Rustaphor/LightRelay4Camping/Sims/LSenseComparator_inverted.cir

[Main]
FileType=CIR
Version=12.00
Program=Micro-Cap
Component Version=10.00
Shape Version=11.00
Screen=1707,960
MCAPVersion=12.2.0.5
Key ID=Demo
NLCnt=60
TXCnt=10

[shapedef]
Name=Arrow
Line=-16,0,24,0
PolyClosed=4
PolyLine=24,0
PolyLine=24,0
PolyLine=16,-4
PolyLine=16,4

[shapedef]
Name=Capacitor
Line=0,0,22,0
Line=22,-8,22,8
Line=26,-8,26,8
Line=26,0,48,0
Current=32,12,16,12

[shapedef]
Name=Fixed
Line=8,0,32,0
Line=8,0,0,-8
Line=8,0,0,8

[shapedef]
Name=Ground
Line=0,0,12,0
Line=12,-8,12,8
Line=18,-4,18,4
Line=24,0,24,0

[shapedef]
Name=Minus.root
Line=-2,0,2,0

[shapedef]
Name=Opamp5
Root="Opamp.root",0,0,0
Root="Plus.root",25,-4,0
Root="Minus.root",25,52,0
Line=32,56,32,34
Line=32,-8,32,13

[shapedef]
Name=Opamp.root
Line=0,48,6,48
Line=0,0,5,0
Line=6,-4,6,52
Line=6,-4,48,24
Line=6,52,48,24
Line=48,24,72,24
Line=10,12,14,12
Line=12,10,12,14
Line=10,36,14,36
Line=4,0,6,0

[shapedef]
Name=Plus.root
Line=-2,0,2,0
Line=0,-2,0,2

[shapedef]
Name=Pot
Line=0,0,12,0
Line=12,0,14,-4
Line=14,-4,18,4
Line=18,4,22,-4
Line=22,-4,26,4
Line=26,4,30,-4
Line=30,-4,34,4
Line=34,4,36,0
Line=36,0,48,0
PolyClosed=4
PolyLine=24,4
PolyLine=24,4
PolyLine=22,8
PolyLine=26,8
Line=24,8,24,16

[shapedef]
Name=Pulse_Source
Root="Vsource.root",0,0,0
Line=20,-4,20,0
Line=20,0,26,0
Line=26,0,26,4

[shapedef]
Name=Resistor
PolyOpen=12
PolyLine=0,0
PolyLine=0,0
PolyLine=12,0
PolyLine=14,-4
PolyLine=18,4
PolyLine=22,-4
PolyLine=26,4
PolyLine=30,-4
PolyLine=34,4
PolyLine=36,0
PolyLine=48,0
PolyLine=48,0
Current=32,8,16,8

[shapedef]
Name=Resistor_Euro
Rectangle=12,-4,36,4
FColor=None
Line=0,0,12,0
Line=48,0,36,0
Current=32,8,16,8

[shapedef]
Name=Vsource.root
Line=0,0,12,0
Line=36,0,48,0
Ellipse=12,-12,36,12
FColor=None
Line=7,5,7,9
Root="Plus.root",41,7,0
Current=32,16,16,16

[compdef]
Name=Resistor
Definition=Resistor
Shape=Resistor
ShapeAlias="Euro","Resistor_Euro"
Mask=6401
Used=284
memo=Resistor
Label Offset=18,6,8,11
PinCnt=2
Pin="Plus",6,0,-10,-4
Pin="Minus",0,0,-14,-4

[compdef]
Name=Arrow
Definition=Blank
Shape=Arrow
Mask=6144
Used=3
memo=Arrow graphic for documentation
Label Offset=-5,4,9,-12
PinCnt=0

[compdef]
Name=Ground
Definition=Ground
Shape=Ground
Mask=257
Used=341
memo=Ground
Label Offset=0,0,0,0
PinCnt=1
Pin="PinA",0,0,-3,-7

[compdef]
Name=Pot
Definition=Macro
Shape=Pot
Mask=4864
Used=5
memo=Potentiometer Macro
Label Offset=32,4,9,11
PinCnt=3
Pin="PINA",a,0,0,-13,-5
Pin="PINB",a,3,2,6,5
Pin="PINC",a,6,0,-12,-5

[compdef]
Name=Fixed Analog
Definition=ANALOG STATE
Shape=Fixed
Mask=2048
Used=3
memo=Provides a fixed DC voltage
Label Offset=-14,-7,-6,-27
PinCnt=1
Pin="Out",4,0,-8,-3

[compdef]
Name=Pulse Source
Definition=Pulse source
Shape=Pulse_Source
Mask=4864
Used=17
memo=Pulse Source
Label Offset=18,13,15,9
PinCnt=2
Pin="Plus",6,0,-5,-4
Pin="Minus",0,0,-19,-4

[compdef]
Name=Capacitor
Definition=Capacitor
Shape=Capacitor
Mask=6401
Used=55
memo=Capacitor
Label Offset=16,12,12,12
PinCnt=2
Pin="Plus",6,0,-3,-5
Pin="Minus",0,0,-14,-5

[compdef]
Name=LMV321_NS
Definition=Subckt
Shape=Opamp5
Mask=4224
Used=3
memo=Single General Purpose, Low Voltage Rail-to-Rail Output Opamp
Label Offset=51,34,-8,44
PinCnt=5
Pin="3",a,0,0,-3,-4
Pin="2",a,0,6,-3,18
Pin="4",a,4,-1,6,15
Pin="5",a,4,7,6,0
Pin="6",a,9,3,-3,-3

[Circuit]
Default Object=Color=#000080,Width=2
Default Object Font=Height=-15,FStyle=0,Color=#000080,Name=Arial
Default Object Apply Border To Text=No
Default Object Apply Fill To Text=No
Default Object GridSnap=No
NodeVoltageFormat=3
CurrentFormat=3
PowerFormat=3
PathDelayFormat=3
WarningFormat=3
GridTextFormulaFormat=3
Window Placement in Transient Analysis=2,3, -1,-1, -8,-31, 104,104,1568,578
Window Placement in DC Analysis=2,3, -1,-1, -8,-31, 26,26,1490,500
SpiceType=AMBIGUOUS
Title_Block_Border=None
Title_Block=False
Show Nodes=False
Show Voltages=False
Show Current=False
Show Power=False
Show Condition=False
Show Pin Connections=False
Show Connection Warnings=False
Show Cross=False
Show Attribute Text=True
Show Grid Text=True

[Comp]
Name=Resistor
Px=232,120
Rot=5

[Attr]
ON=7,-37,PART
V=R1
Style=8192

[Attr]
ON=7,-24,RESISTANCE
V=V(V_Light)*1000
Style=8192

[Attr]
ON=0,88,SHAPEGROUP
V=Euro

[Attr]
ON=0,0,PACKAGE
V

[Comp]
Name=Arrow
Px=192,104

[Attr]
ON=-17,-16,TEXT
V=Light
Style=8192

[Wire]
Pxs=232,48,232,72

[Comp]
Name=Resistor
Px=232,272
Rot=1

[Attr]
ON=8,11,PART
V=R3
Style=8192

[Attr]
ON=8,25,RESISTANCE
V=180k
Style=8192

[Attr]
ON=0,33,MODEL
V=C6_1%

[Attr]
ON=0,0,PACKAGE
V=C6

[Comp]
Name=Ground
Px=496,240
Rot=1

[Wire]
Pxs=496,48,496,176

[Wire]
Pxs=232,48,432,48

[Comp]
Name=Arrow
Px=192,88

[Attr]
ON=-17,-16,TEXT
V
Style=8192

[Comp]
Name=Resistor
Px=232,144
Rot=1

[Attr]
ON=8,11,PART
V=R2
Style=8192

[Attr]
ON=8,25,RESISTANCE
V=10k
Style=8192

[Attr]
ON=0,33,MODEL
V=C6_1%

[Attr]
ON=0,0,PACKAGE
V=C6

[Comp]
Name=Pot
Px=232,256
Rot=3

[Attr]
ON=-26,-38,PART
V=X1
Style=8192

[Attr]
ON=-30,-39,FILE
V=Pot

[Attr]
ON=-39,-26,Param:POTSIZE
V=180k
Style=8192

[Attr]
ON=-25,-81,Param:PERCENT
V=L_POT

[Attr]
ON=0,0,PACKAGE
V

[Comp]
Name=Ground
Px=232,344
Rot=1

[Wire]
Pxs=248,232,296,232

[Comp]
Name=Fixed Analog
Px=160,48

[Attr]
ON=-14,-7,PART
V=V2

[Attr]
ON=-12,-5,VALUE
V=5
Style=8192

[Attr]
ON=0,0,PACKAGE
V

[Comp]
Name=Pulse Source
Px=96,120
Rot=3

[Attr]
ON=-31,-23,PART
V=V1
Style=8192

[Attr]
ON=-70,-37,MODEL
V=IMPULSE

[Attr]
ON=0,0,PACKAGE
V

[Comp]
Name=Ground
Px=96,120
Rot=1

[Wire]
Pxs=96,56,96,72

[Wire]
Pxs=192,48,232,48

[Wire]
Pxs=296,232,312,232

[Wire]
Pxs=232,256,232,264

[Wire]
Pxs=232,192,232,200

[Wire]
Pxs=232,120,232,144

[Wire]
Pxs=232,320,232,344

[Wire]
Pxs=536,208,544,208

[Comp]
Name=Resistor
Px=432,96
Rot=1

[Attr]
ON=8,11,PART
V=R4
Style=8192

[Attr]
ON=8,25,RESISTANCE
V=100k
Style=8192

[Attr]
ON=8,39,MODEL
V=C6_1%

[Attr]
ON=0,0,PACKAGE
V=C6

[Comp]
Name=Resistor
Px=432,272
Rot=1

[Attr]
ON=-26,11,PART
V=R5
Style=8192

[Attr]
ON=-36,24,RESISTANCE
V=82k
Style=8192

[Attr]
ON=8,39,MODEL
V=C6_1%

[Attr]
ON=0,0,PACKAGE
V=C6

[Wire]
Pxs=432,144,432,184

[Wire]
Pxs=432,48,432,96

[Wire]
Pxs=432,48,496,48

[Comp]
Name=Ground
Px=432,344
Rot=1

[Wire]
Pxs=432,320,432,344

[Wire]
Pxs=432,184,464,184

[Wire]
Pxs=432,184,432,272

[Comp]
Name=Resistor
Px=464,272

[Attr]
ON=18,6,PART
V=R6
Style=8192

[Attr]
ON=18,20,RESISTANCE
V=1Meg
Style=8192

[Attr]
ON=18,34,MODEL
V=C6_1%

[Attr]
ON=0,0,PACKAGE
V=C6

[Wire]
Pxs=544,208,544,272

[Wire]
Pxs=512,272,544,272

[Wire]
Pxs=432,272,456,272

[Comp]
Name=Capacitor
Px=472,320
Rot=4

[Attr]
ON=31,2,PART
V=C1
Style=8192

[Attr]
ON=49,2,CAPACITANCE
V=56p
Style=8192

[Attr]
ON=0,0,PACKAGE
V

[Wire]
Pxs=456,272,456,320

[Wire]
Pxs=456,320,472,320

[Wire]
Pxs=456,272,464,272

[Wire]
Pxs=520,320,544,320

[Wire]
Pxs=544,272,544,320

[Comp]
Name=Capacitor
Px=376,272
Rot=1

[Attr]
ON=-28,9,PART
V=C3
Style=8192

[Attr]
ON=-37,22,CAPACITANCE
V=100n
Style=8192

[Attr]
ON=0,0,PACKAGE
V

[Comp]
Name=Ground
Px=376,344
Rot=1

[Wire]
Pxs=376,184,376,272

[Wire]
Pxs=376,184,432,184

[Wire]
Pxs=376,320,376,344

[Comp]
Name=Capacitor
Enable=FALSE
Px=312,272
Rot=1

[Attr]
ON=-29,10,PART
V=C2
Style=8192

[Attr]
ON=-34,24,CAPACITANCE
V=100n
Style=8192

[Attr]
ON=0,0,PACKAGE
V

[Wire]
Pxs=312,232,312,272

[Wire]
Pxs=312,232,464,232

[Comp]
Name=Ground
Px=312,344
Rot=1

[Wire]
Pxs=312,320,312,344

[Comp]
Name=LMV321_NS
Px=464,184

[Attr]
ON=51,34,PART
V=X3
Style=8192

[Attr]
ON=51,48,NAME
V=LMV321_NS

[Attr]
ON=51,76,PACKAGE
V=SC70_5

[Comp]
Name=Resistor
Enable=FALSE
Px=168,208
Rot=1

[Attr]
ON=-28,9,PART
V=R7
Style=8192

[Attr]
ON=-39,25,RESISTANCE
V=1.8Meg
Style=8192

[Attr]
ON=8,39,MODEL
V=C6_1%

[Attr]
ON=8,67,PACKAGE
V=C6

[Wire]
Pxs=168,200,168,208

[Wire]
Pxs=168,200,232,200

[Wire]
Pxs=232,200,232,208

[Wire]
Pxs=168,256,168,264

[Wire]
Pxs=168,264,232,264

[Wire]
Pxs=232,264,232,272

[Grid Text]
Text="3"
Px=456,200
GridSnap=True
JustifyH=Left
JustifyV=Bottom
CBorder=None

[Grid Text]
Text="2"
Px=456,248
GridSnap=True
JustifyH=Left
JustifyV=Bottom
CBorder=None

[Grid Text]
Text="1"
Px=512,200
GridSnap=True
JustifyH=Left
JustifyV=Bottom
CBorder=None

[Grid Text]
Text="1/2 LMV358"
Px=432,168
GridSnap=True
JustifyH=Left
JustifyV=Bottom
CBorder=None

[Grid Text]
Text="Ref"
Px=432,184
GridSnap=True
JustifyH=Left
JustifyV=Bottom
CBorder=None

[Grid Text]
Text="GL5516"
Px=304,88
GridSnap=True
JustifyH=Right
JustifyV=Bottom
CBorder=None

[Grid Text]
Text="V_Light"
Px=96,56
GridSnap=True
JustifyH=Center
JustifyV=Bottom
CBorder=None

[Grid Text]
Text="SET_lvl"
Px=296,232
GridSnap=True
JustifyH=Right
JustifyV=Bottom
CBorder=None

[Grid Text]
Text="Out"
Px=544,208
GridSnap=True
JustifyH=Left
JustifyV=Bottom
CBorder=None

[Grid Text]
Text="VCC"
Px=232,48
GridSnap=True
JustifyH=Left
JustifyV=Bottom
CBorder=None

[Schematic]
CurrentSection 0=0
CurrentSection 1=0
CurrentSection 2=0
CurrentSection 3=0
Splitter.xs=0
Splitter.ys=0
TextQuad=4099
Scale=0.66666666666666663
GridType=Normal
GridUser=10
ShapeGroups="Main","Euro","Polarity","Main1","Main11","Electrolytic","GroundArrow","DeMorgan"
CalcRMS=False
CalcAVG=False
CalcPeak=False
CalcVoltage=True
DisplayMeasure=Last
ShareScales=True

[Tools]
Pos=Top
FILESAVEASOLD=No
BOM=No
FILEPCB=No
PROBE=Yes
SELECT=Yes
PAN=Yes
COMP=Yes
TEXT=Yes
WIRE=Yes
WIRED=Yes
BUS=Yes
GRAPHIC=Yes
FLOWCHART=Yes
LINE=No
ELLIPSE=No
RECT=No
DIAM=No
ARC=No
PIE=No
TRIANGLE=No
STAR=No
LEFTBRK=No
RIGHTBRK=No
BOTHBRK=No
META=Yes
PARALLELOGRAM=No
FC_PROCESS=No
FC_ALT_PROCESS=No
FC_DECISION=No
FC_DATA=No
FC_PREDEFPROCESS=No
FC_INTERNALSTORAGE=No
FC_DOCUMENT=No
FC_MULTIDOCUMENT=No
FC_TERMINATOR=No
FC_PREPARATION=No
FC_MANUALINPUT=No
FC_MANUALOPERATION=No
FC_CONNECTOR=No
FC_OFFPAGECONNECTOR=No
FC_PUNCHCARD=No
FC_PUNCHEDTAPE=No
FC_SUMMING_JUNCTION=No
FC_OR=No
FC_COLLATE=No
FC_SORT=No
FC_EXTRACT=No
FC_MERGE=No
FC_STORED_DATA=No
FC_DELAY=No
FC_SAS=No
FC_MAGNETIC_DISK=No
FC_DAS=No
FC_DISPLAY=No
SPREAD_SHEET=Yes
POLYCLOS=No
POLYOPEN=No
FLAG=Yes
INFO=Yes
HELP=Yes
HELP_SPICE=No
LINK=Yes
CHECK=Yes
REGION_ENABLE=Yes
TITLE_BLOCK=Yes
DIGTRC=No
DIGTRC2=No
BUILD_COMMAND=Yes
DIGALL=No
GRIDTEXT=Yes
COMPTEXT=Yes
NODE=Yes
MEASURED=Yes
NODEV=Yes
CURRENT=Yes
POWER=Yes
CONDITIN=Yes
PIN=Yes
CONNWARN=Yes
CROSS=No
GRID=Yes
BORDER=Yes
BORDERONE=Yes
TITLE=Yes
RUBBER=Yes
PROPERTY=Yes
STEP=Yes
MIRROR=Yes
ROTATE=Yes
FLIPY=Yes
FLIPX=Yes
CIR_MAKEMACRO=No
CLEARCUTWIRE=No
CLIPBOARDCIRPAGE2BMM=No
FINDCOMP=Yes
FIND=Yes
REPEAT=No
REPLACE=No
MODEL=Yes
CIR2CKT=No
ATTDISP=No
ENABLE=Yes
DISABLE=Yes
ENABLE_WITH=Yes
TOFRONT=Yes
TOBACK=Yes
SELNEXT=No
PAGEADD=No
PAGEADDTEXT=No
ADDSECTION=No
PAGEDEL=No
ZOOMIN=Yes
ZOOMOUT=Yes
AUTOSCALECIR=Yes
GOTOFLAG=No
UPLEVEL=Yes
COLOR=Yes
FONT=Yes
STYLE=Yes
DM_LAST=No
DM_RMS=No
DM_AVG=No
DM_PEAK=No
GRID_NONE=No
GRID_NORMAL=No
GRID_BOLD_5=No
GRID_BOLD_6=No
GRID_BOLD_USER=No
GRAPH_PAPER=No
SPLITCIRTEXTH=No
SPLITCIRTEXTV=No
SPACE_SPLITTERS_EVENLY=No
NORMALCIR=No
RENAMEDEFINE=No
RENAMECMP=No
ATTALIGN=No
RESETNODEPOS=No
FIT2STANDARD=No
NODESNAP=No
MOVETEXT=No
TEXTINC=No
TOGGLETEXT=No
TOGGLEMODE=No
TOLERANCE=No
ALIGNAB=No
ALIGNLEFT=No
ALIGNCENTER=No
ALIGNRIGHT=No
ALIGNTOP=No
ALIGNMIDDLES=No
ALIGNBOTTOM=No

[Section]
Index=0
Name="LSenseComparator"
Type=Main
Enable=True
CurrentPage 0=0
CurrentPage 1=0
CurrentPage 2=0
CurrentPage 3=0
TabSize 0=425
TabSize 1=425
TabSize 2=425
TabSize 3=425

[Page]
Index=0
Section=0
Print=True
Enable=True
Name=Main
PrinterScale=1
Scale 0=1
Scale 1=1
Scale 2=1
Scale 3=0.66666666666666663
Px=127,162
WinBackGround Color=#F8F5E9
Select Color=#FF0000
Anchor Color=#000000
Select Box Color=#000080
Grid Text Color=Height=-12,FStyle=0,Color=#0000FF,Name=Verdana
Grid Text RTF=False
Grid Text Angle=0
Grid Text GridSnap=True
Grid Text PinIt=False
Grid Text JustifyH=Left
Grid Text JustifyV=Bottom
Grid GradientColor2=None
Grid OutlineThickness=1
Grid OutlineColor=None
Component Color=#0000FF
Attribute Text=Height=-12,FStyle=0,Color=#008000,Name=Verdana
Wire Color=#008000
Bus Color=#008000
Pin Connection=Height=-10,FStyle=0,Color=#FF0000,Name=Arial
Pin Marker Color=#008000
Node Number=Height=-11,FStyle=0,Color=#FF00FF,Name=Arial
Node Voltage Color=Height=-11,FStyle=0,Color=#000000,Name=Arial
Dynamic AC Voltage Color=#E4E4E4
Text Banner Text=Height=-15,FStyle=0,Color=#800000,Name=Arial
Title Block Background=#C0C0C0
Current=Height=-11,FStyle=0,Color=#0000FF,Name=Arial
Power/Condition=Height=-11,FStyle=0,Color=#FF0000,Name=Arial
Digital Path Color=#FF0000
Title Block Border=#000000
Disabled	Color=#C0C0C0
Search Color=#FFFF00
Grid Color=#000000
Graph Paper=#E4E4E4
Digital 0 Color=#000000
Digital R Color=#FFFF00
Digital F Color=#FFFF00
Digital 1 Color=#FF0000
Digital X Color=#C0C0C0
Digital Z Color=#808080
Block Select Color=#51F998

[Page]
Index=1
Section=0
Type=Text
Print=False
Enable=True
Name=Text
Font=Height=-15,FStyle=0,Color=#000000,Name=Courier New
Comment Color=#008000
WinBackGround Color=#FFFFFF
Disabled	Color=#C0C0C0
KeyWord Color=#0000FF
Error	Color=#FF0000
Search Color=#FFFF00

[Page]
Index=2
Section=0
Type=Text
Print=False
Enable=True
Name=Models
Font=Height=-15,FStyle=0,Color=#000000,Name=Courier New
Comment Color=#008000
WinBackGround Color=#FFFFFF
Disabled	Color=#C0C0C0
KeyWord Color=#0000FF
Error	Color=#FF0000
Search Color=#FFFF00

[Page]
Index=3
Section=0
Type=Info
Print=False
Enable=True
Name=Info
Font=Height=-15,FStyle=0,Color=#000000,Name=Courier New
Comment Color=#008000
WinBackGround Color=#FFFFFF
Disabled	Color=#C0C0C0
KeyWord Color=#0000FF
Error	Color=#FF0000
Search Color=#FFFF00

[Text Area]
Section=0
Page=1
Text=.define L_POT 50	; Позиция посередине
Text=
Text=; Настройки фоторезистора
Text=.param Rph_max=470k	; Максимальный порог яркости включения фотореле
Text=.param Rph_min=5k	; Максимальный порог яркости отключения фотореле
Text=
Text=.STEP LIN L_POT 0 100 100

[Text Area]
Section=0
Page=2
Text=* Schematic File
Text=*
Text=* Syntax:
Text=* .MODEL <model name> [AKO:<reference model name>] <ModelType>
Text=* +([<parameter name>=<value>][LOT[/#][/GAUSS|/UNIFORM|/WCASE]=[<tol>[%]] |[-<low>%,<high>%]][DEV[/#][/GAUSS|/UNIFORM|/WCASE]=[<tol>[%]]...)
Text=* ModelType must be one of OPA,D,NPN,NMOS,NJF,PUL,SIN,TRN,CORE,GASFET,VSWITCH,ISWITCH,CAP,IND,RES,PNP,PMOS,PJF,DOUTPUT,DINPUT,UADC,UDAC,UGATE,UTGATE,UEFF,UGFF,UDLY,UPLD,UROM,URAM,UBGT,UIO,LPNP,NIGBT,I,V
Text=*
Text=*Examples:
Text=* .MODEL 2N2222A NPN(BF=150 IS=1E-14)
Text=* .model M1 NMOS(KP=2.5E-5 VTO=1.345 CGDO=14.67p CGBO=4.566p)
Text=* .MODEL DK D(IS=1E-18)
Text=* .model 2N2222A AKO:2N2222 NPN (BF=55 ISE=10F)
Text=* .Model BJT1 NPN (RE=12 LOT/1/GAUSS=30% DEV/2/UNIFORM=2%)
Text=*
Text=* A .cir file is typically found in the data directory
Text=*
Text=*** From file C:\Games\MicroCap12\library\UTILITY.LBR
Text=*** 1ns Impulse Source
Text=.MODEL IMPULSE PUL (P1=0 P2=10 P3=10 P4=20 P5=20 VONE={Rph_max/1000}
Text=+ VZERO={Rph_min/1000})
Text=*** From file C:\Games\MicroCap12\library\UTILITY.LBR
Text=*** 5V Sawtooth Wave
Text=.MODEL SAWTOOTH PUL (P1=0 P2=2 P3=2 P4=3 P5=3)
Text=*** From file C:\Games\MicroCap12\library\UTILITY.LBR
Text=*** 5V Triangle Wave
Text=.MODEL TRIANGLE PUL (P1=0 P2=10 P3=10 P4=10 P5=10)

[InfoPage]
InfoPage=True
Warnings=True
System=True
Defines=True
Array=True
Model=True
Measure=True
MacroSubckt=True
NotUsed=True
ComponentCounts=True
VariablizePaths=False
DontShowPaths=False
SimulationLog=True

[Transient]
WinID=1
Window Placement=2,3, -1,-1, -8,-31, 104,104,1568,578
Font=Height=-19,FStyle=0,Color=#0000FF,Name=Arial
WinBackGround Color=#FFFFFF
Select Color=#FF0000
Anchor Color=#000000
Select Box Color=#000080
Title=PhotoRes.cir
AutoTitle=Yes
Grid Color=#808080
Grid Weight=1
Grid Pattern=Dot6
Tracker Foreground=Height=-15,FStyle=0,Color=#000000,Name=Arial
Tracker Background=#FFFF00
Baseline color=#0000FF
BaseLine Weight=1
CurveFit color=#FF0000
CurveFit Weight=2
CurveFit Pattern=Dash
Static Grids=False
PlusMark=False
MinorLog25=Off
LabelMinor=Off
DataPoints=False
Token=False
Ruler=False
XAxisGrids=True
YAxisGrids=True
MinorLogGrids=True
BaseLine=False
AlignZ=True
Align Cursors=True
TagFormatX=3
TagFormatY=3
FormulaFormat=2
EndMode=SCALE
Graph Background=#FFFFFF
Tracker Intercept=True
Tracker Mouse=True
Tracker Cursor=True
Tracker Cursor BranchInfo=False
Horizontal Cursor=False
Same Y Scales=Yes
Enable X Scaling=True
Enable Y Scaling=True
Keep X Scales The Same=True
Number of Grids X=5
Number of Grids Y=5
Cursor Select Color Primary=#C0C0C0
Cursor Select Color Secondary=#FF0000
Data Point Labels Color Fore=Height=-15,FStyle=0,Color=#000000,Name=Arial
Data Point Labels Color Back=#FFFF00
OperPoint=True
OperPointOnly=False
AutoScaleRanges=False
FixedTimeStep=False
DoPSS=False
PSS_Periods="1"
PSS_Iterations="5"
PSS_Error="1u"
PSS_ShowPlots=True
FFT_NPts="8192"
FFT_IncludeDCHarmonic=False
FFT_AutoScale_Harmonics="10"
PrinterAutoTile=No
PrinterBlackBorder=No
MonMaxShow=5
MonPageWidth=66
MonPlotWidth=21
MonExprXWidth=142
MonExprYWidth=367
MonRangeXWidth=90
MonRangeYWidth=90
AnimateWait=None
AnimateWaitTime=500
AnimatePressAfter=0
Save_For_Future=No
Reduce_Display=1
Reduce_Save=1
Reduce_ThrowDataOut=0
Num Out Header Left
Num Out Header Center="$MC\n$user\n$company\n$Analysis of $name\n$date $time"
Num Out Header Right
Num Out Delimiter=32
Num Out Write=True
Num Out Write Main Header=True
Num Out Write Limits=True
Num Out Write Branch Header=True
Num Out Write Models=False
Num Out Write Zero Models=True
Num Out Write Undefined Models=True
Num Out Write Operating Point=True
Num Out Write Measurement Values=True
Num Out Write Tolerance Detail=True
Num Out Write Values=True
Num Out Write Waveform Header=True
Num Out Allow Dup Y Expr=False
Num Out Low="TSTART"
Num Out High="TMAX"
Num Out Font=Height=-15,FStyle=0,Color=#000000,Name=Courier New
Num Out Format=3
Num Out HideNonSelected=False
Num Out UseActualDataPoints=False
AutoSaveWave=False
Wave Format=16E
State Variables Format=5E
Print Individual Pages=False

[Tools]
Pos=Top
SELECT=Yes
PAN=Yes
GRAPHIC=Yes
LINE=No
ELLIPSE=No
RECT=No
DIAM=No
ARC=No
PIE=No
TRIANGLE=No
STAR=No
LEFTBRK=No
RIGHTBRK=No
BOTHBRK=No
META=Yes
PARALLELOGRAM=No
POLYCLOS=No
POLYOPEN=No
SCALE=Yes
CURSOR=Yes
MEASUREH=Yes
MEASUREV=Yes
TAG=Yes
PTAG=Yes
TEXT=Yes
PROPERTY=Yes
START=Yes
STOP=Yes
PAUSE=Yes
RESUME=No
DATAPTS=Yes
TOKENS=Yes
RULER=Yes
PLUS=Yes
XAXIS=Yes
YAXIS=Yes
MINORLOG=Yes
LOG25=Yes
BASELINE=Yes
HORIZCUR=Yes
GOTOX=Yes
GOTOY=Yes
GOTOPERF=Yes
GOTOBRNC=Yes
CLEAR_ACCUMULATED=Yes
PDELETE_ALL_PLOTS=Yes
NEXT=Yes
NEXTIN=Yes
PEAK=Yes
VALLEY=Yes
HIGH=Yes
LOW=Yes
INFLECTN=Yes
GHIGH=Yes
GLOW=Yes
BOTTOM=Yes
TOP=Yes
WAVEFORMBUFFER=Yes
AOUTPUT=Yes
PKEY=Yes
ENXSCALE=Yes
ENYSCALE=Yes
ZOOMIN=Yes
ZOOMOUT=Yes
AUTOSCALE=Yes
RESTORESCALE=No
COLOR=Yes
FONT=Yes
STYLE=Yes
SELNEXT=No
NORMALIZE=No
NORMALIZE_MIN=No
NORMALIZE_MAX=No
ADD_TAG_LEFT=No
ADD_TAG_RIGHT=No
ADD_HORZ_TAG=No
ADD_VERT_TAG=No
ALIGN_CURSORS=No
ALIGN_CURSORSZ=No
CURSORTOCLIPBOARD=No
TRACKER_CURSOR=No
TRACKER_CURSOR_BRANCHINFO=No
TRACKER_INTERCEPT=No
TRACKER_MOUSE=No
TOFRONT=Yes
TOBACK=Yes
SPLITCIRTEXTH=No
SPLITCIRTEXTV=No
SPACE_SPLITTERS_EVENLY=No
NORMALCIR=No
LABEL_WAVEFORM=No
LABEL_DATA_POINTS=No
WFB_ADD_TO_LIMITS=No
ENVELOPE=No
SAMEYSCALES=No
KEEPXSCALESTHESAME=No
CURVEFIT=No
ADD_MARKER=No
SHOWWATCH=No
BP=No
TOGGLEMODE=No
REMOVEALLTEXT=No
AUTOSCALEX=No
LABELALLMINOR=No
ALIGNLEFT=No
ALIGNCENTER=No
ALIGNRIGHT=No
ALIGNTOP=No
ALIGNMIDDLES=No
ALIGNBOTTOM=No

[APage]
Analysis=Transient
Name="MAIN"

[DC]
WinID=3
Window Placement=2,3, -1,-1, -8,-31, 26,26,1490,500
Font=Height=-19,FStyle=0,Color=#0000FF,Name=Arial
WinBackGround Color=#FFFFFF
Select Color=#FF0000
Anchor Color=#000000
Select Box Color=#000080
Title=PhotoRes.cir
AutoTitle=Yes
Grid Color=#808080
Grid Weight=1
Grid Pattern=Dot6
Tracker Foreground=Height=-15,FStyle=0,Color=#000000,Name=Arial
Tracker Background=#FFFF00
Baseline color=#0000FF
BaseLine Weight=1
CurveFit color=#FF0000
CurveFit Weight=2
CurveFit Pattern=Dash
Static Grids=False
PlusMark=False
MinorLog25=Off
LabelMinor=Off
DataPoints=False
Token=False
Ruler=False
XAxisGrids=True
YAxisGrids=True
MinorLogGrids=True
BaseLine=False
AlignZ=True
Align Cursors=True
TagFormatX=3
TagFormatY=3
FormulaFormat=2
EndMode=SCALE
Graph Background=#FFFFFF
Tracker Intercept=False
Tracker Mouse=True
Tracker Cursor=True
Tracker Cursor BranchInfo=False
Horizontal Cursor=False
Same Y Scales=Yes
Enable X Scaling=True
Enable Y Scaling=True
Keep X Scales The Same=True
Number of Grids X=5
Number of Grids Y=5
Cursor Select Color Primary=#C0C0C0
Cursor Select Color Secondary=#FF0000
Data Point Labels Color Fore=Height=-15,FStyle=0,Color=#000000,Name=Arial
Data Point Labels Color Back=#FFFF00
AutoScaleRanges=False
PrinterAutoTile=No
PrinterBlackBorder=No
MonMaxShow=2
MonPageWidth=66
MonPlotWidth=21
MonExprXWidth=142
MonExprYWidth=286
MonRangeXWidth=90
MonRangeYWidth=90
AnimateWait=None
AnimateWaitTime=500
AnimatePressAfter=0
ThumbNail=816,211,1111,403
Save_For_Future=No
Reduce_Display=1
Reduce_Save=1
Reduce_ThrowDataOut=0
Num Out Header Left
Num Out Header Center="$MC\n$user\n$company\n$Analysis of $name\n$date $time"
Num Out Header Right
Num Out Delimiter=32
Num Out Write=True
Num Out Write Main Header=True
Num Out Write Limits=True
Num Out Write Branch Header=True
Num Out Write Models=False
Num Out Write Zero Models=True
Num Out Write Undefined Models=True
Num Out Write Measurement Values=True
Num Out Write Tolerance Detail=True
Num Out Write Values=True
Num Out Write Waveform Header=True
Num Out Allow Dup Y Expr=False
Num Out Low="DCMIN"
Num Out High="DCMAX"
Num Out Font=Height=-15,FStyle=0,Color=#000000,Name=Courier New
Num Out Format=3
Num Out HideNonSelected=False
Num Out UseActualDataPoints=False
AutoSaveWave=False
Wave Format=16E
State Variables Format=5E
Print Individual Pages=False

[Tools]
Pos=Top
SELECT=Yes
PAN=Yes
GRAPHIC=Yes
LINE=No
ELLIPSE=No
RECT=No
DIAM=No
ARC=No
PIE=No
TRIANGLE=No
STAR=No
LEFTBRK=No
RIGHTBRK=No
BOTHBRK=No
META=Yes
PARALLELOGRAM=No
POLYCLOS=No
POLYOPEN=No
SCALE=Yes
CURSOR=Yes
MEASUREH=Yes
MEASUREV=Yes
TAG=Yes
PTAG=Yes
TEXT=Yes
PROPERTY=Yes
START=Yes
STOP=Yes
PAUSE=Yes
RESUME=No
DATAPTS=Yes
TOKENS=Yes
RULER=Yes
PLUS=Yes
XAXIS=Yes
YAXIS=Yes
MINORLOG=Yes
LOG25=Yes
BASELINE=Yes
HORIZCUR=Yes
GOTOX=Yes
GOTOY=Yes
GOTOPERF=Yes
GOTOBRNC=Yes
CLEAR_ACCUMULATED=Yes
PDELETE_ALL_PLOTS=Yes
NEXT=Yes
NEXTIN=Yes
PEAK=Yes
VALLEY=Yes
HIGH=Yes
LOW=Yes
INFLECTN=Yes
GHIGH=Yes
GLOW=Yes
BOTTOM=Yes
TOP=Yes
WAVEFORMBUFFER=Yes
AOUTPUT=Yes
PKEY=Yes
ENXSCALE=Yes
ENYSCALE=Yes
ZOOMIN=Yes
ZOOMOUT=Yes
AUTOSCALE=Yes
RESTORESCALE=No
COLOR=Yes
FONT=Yes
STYLE=Yes
SELNEXT=No
NORMALIZE=No
NORMALIZE_MIN=No
NORMALIZE_MAX=No
ADD_TAG_LEFT=No
ADD_TAG_RIGHT=No
ADD_HORZ_TAG=No
ADD_VERT_TAG=No
ALIGN_CURSORS=No
ALIGN_CURSORSZ=No
CURSORTOCLIPBOARD=No
TRACKER_CURSOR=No
TRACKER_CURSOR_BRANCHINFO=No
TRACKER_INTERCEPT=No
TRACKER_MOUSE=No
TOFRONT=Yes
TOBACK=Yes
SPLITCIRTEXTH=No
SPLITCIRTEXTV=No
SPACE_SPLITTERS_EVENLY=No
NORMALCIR=No
LABEL_WAVEFORM=No
LABEL_DATA_POINTS=No
WFB_ADD_TO_LIMITS=No
ENVELOPE=No
SAMEYSCALES=No
KEEPXSCALESTHESAME=No
CURVEFIT=No
ADD_MARKER=No
SHOWWATCH=No
BP=No
TOGGLEMODE=No
REMOVEALLTEXT=No
AUTOSCALEX=No
LABELALLMINOR=No
ALIGNLEFT=No
ALIGNCENTER=No
ALIGNRIGHT=No
ALIGNTOP=No
ALIGNMIDDLES=No
ALIGNBOTTOM=No

[APage]
Analysis=DC
Name="MAIN"

[Monte Carlo Options]
Analysis=Transient
Status=Off
Zero Tolerance=False
Eliminate Outliers=False
Distribution=Normal
Number of Runs=10
Seed=0

[Monte Carlo Options]
Analysis=DC
Status=Off
Zero Tolerance=False
Eliminate Outliers=False
Distribution=Normal
Number of Runs=10
Seed=0

[Limits]
Analysis=Transient
TMax=20
TStart=0
TStep=10m
NPts=51
Temp=27
RetraceRuns=1
StateVar=Zero
RunOption=Normal
Temperature Type=Linear
Accumulate Plots=False
IgnoreExprErrors=False

[WaveForm]
Analysis=Transient
Plt=1
AliasID=1
XExp=T
YExp=R(R1),Photoresistor R1 (Ohms)
XRng=20
YRng=600000
Options=LINEARX,LINEARY
Range Grid X=4
Range Grid Y=120000
Enable=Enable
CS=Normal
Line Color=#0000FF
Text Color=#0000FF
Rainbow=False
VFmtX=3
VFmtY=3
ScaleFactorX="None"
ScaleFactorY="None"
ScaleUnitsX="Auto"
ScaleUnitsY="Auto"
SFmtX=2
SFmtY=2
NOFmtX=3E
NOFmtY=3E

[WaveForm]
Analysis=Transient
Plt=2
AliasID=6
XExp=T
YExp=V(Ref)
XRng=20
YRng=5.5,0
Options=LINEARX,LINEARY
Range Grid X=4
Range Grid Y=1.0
Enable=Enable
CS=Normal
Line Color=#202020
Text Color=#202020
Pattern=Dash
Rainbow=False
LWdth=2
VFmtX=3
VFmtY=3
ScaleFactorX="None"
ScaleFactorY="None"
ScaleUnitsX="Auto"
ScaleUnitsY="Auto"
SFmtX=2
SFmtY=2
NOFmtX=3E
NOFmtY=3E

[WaveForm]
Analysis=Transient
Plt=2
AliasID=4
XExp=T
YExp=V(SET_lvl)
XRng=20,0
YRng=5.5,0
Options=LINEARX,LINEARY
Range Grid X=4
Range Grid Y=1.0
Enable=Enable
CS=Normal
Line Color=#7940BF
Text Color=#7940BF
Rainbow=False
VFmtX=3
VFmtY=3
ScaleFactorX="None"
ScaleFactorY="None"
ScaleUnitsX="Auto"
ScaleUnitsY="Auto"
SFmtX=2
SFmtY=2
NOFmtX=3E
NOFmtY=3E

[WaveForm]
Analysis=Transient
Plt=2
AliasID=3
XExp=T
YExp=V(Out),Comparator output
XRng=20,0
YRng=5.5,0
Options=LINEARX,LINEARY
Range Grid X=4
Range Grid Y=1.0
Enable=Enable
CS=Normal
Line Color=#800000
Text Color=#800000
Rainbow=False
VFmtX=3
VFmtY=3
ScaleFactorX="None"
ScaleFactorY="None"
ScaleUnitsX="Auto"
ScaleUnitsY="Auto"
SFmtX=2
SFmtY=2
NOFmtX=3E
NOFmtY=3E

[WaveForm]
Analysis=Transient
Plt=3
AliasID=7
XExp=T
YExp=I(Rn),Load (Ampers)
XRng=20,0
YRng=2.25,-5.25
Options=LINEARX,LINEARY
Range Grid X=4
Range Grid Y=1.5
Enable=DontRun
Line Color=#FF0000
Text Color=#FF0000
Rainbow=False
VFmtX=3
VFmtY=3
ScaleFactorX="None"
ScaleFactorY="None"
ScaleUnitsX="Auto"
ScaleUnitsY="Auto"
SFmtX=2
SFmtY=2
NOFmtX=3E
NOFmtY=3E

[Limits]
Analysis=DC
I1Range=Rph_min,Rph_max,10000
I1=R1
NPts=51
Temp=27
MaxChng=5
StateVar=Zero
RunOption=Normal
Temperature Type=Linear
Accumulate Plots=False
IgnoreExprErrors=False
Sweep1 type=Linear
Sweep2 type=None

[WaveForm]
Analysis=DC
Plt=1
AliasID=1
XExp=DCINPUT1,Rhotoresistor R1 (Ohms)
YExp=V(SET_lvl)
XRng=Rph_max,Rph_min
YRng=5,0
Options=LINEARX,LINEARY
Range Grid Y=1
Enable=Enable
CS=Normal
Line Color=#0000FF
Text Color=#0000FF
Rainbow=False
VFmtX=3
VFmtY=3
ScaleFactorX="None"
ScaleFactorY="None"
ScaleUnitsX="Auto"
ScaleUnitsY="Auto"
SFmtX=2
SFmtY=2
NOFmtX=3E
NOFmtY=3E

[WaveForm]
Analysis=DC
Plt=1
AliasID=2
XExp=DCINPUT1,1/2 VCC (V)
YExp=V(VCC)/2,Reset level LMC555
XRng=Rph_max,Rph_min
YRng=5,0
Options=LINEARX,LINEARY
Range Grid Y=1
Enable=Enable
CS=Normal
Line Color=#000000
Text Color=#000000
Pattern=Dash6
Rainbow=False
LWdth=3
VFmtX=3
VFmtY=3
ScaleFactorX="None"
ScaleFactorY="None"
ScaleUnitsX="Auto"
ScaleUnitsY="Auto"
SFmtX=2
SFmtY=2
NOFmtX=3E
NOFmtY=3E

[Limits]
Analysis=DynamicAC
FirstValueDisplay=Mag
SecondValueDisplay=PhaseDeg
PlaceText=True

[Limits]
Analysis=DynamicDC
Temp=27
SliderPer=10
PlaceText=True

[Pane]
Analysis=Transient
CurrentPage 0="MAIN"

[Pane]
Analysis=AC

[Pane]
Analysis=DC
CurrentPage 0="MAIN"

[Pane]
Analysis=HmDistortion

[Pane]
Analysis=ImDistortion

[Pane]
Analysis=Stability

[Stepping]
Analysis=Transient
Index=1
Status=On
Parameter Type=Symbolic
Name=L_POT
From=0
To=100
Value=100

[Stepping]
Analysis=Transient
Index=2
Parameter Type=Symbolic
From=0
To=100
Value=100

[Stepping]
Analysis=DC
Index=1
Status=On
Parameter Type=Symbolic
Name=L_POT
From=0
To=100
Value=100

[Stepping]
Analysis=DC
Index=2
Parameter Type=Symbolic

[Optimize]
Analysis=Transient
Format=6
ThatCnt=10
POWELL_TOL=1e-4
POWELL_RelPercentTol=.1
POWELL_PercentTol=1m
HOOKE_TOL=1e-4
HOOKE_PercentTol=1m
HOOKE_RHO=.3
HOOKE_EPSILON=1e-9
HOOKE_ITERMAX=1000
DE_MAXITER=200
DE_IPRINT=50
DE_PCROS=.9
DE_FACT=.5
DE_MULTIPLIER=5
InitialRangeFactor=2
InitializeEach=False
Method=Powell
Method=Hooke
Method=LM
Method=DE
Update_Plot=False
Minimize_Plot=False
StartWith=Existing
GridSize=4
NumberOfTrys=10
Log=False
Show Log=False

[Optimize]
Analysis=DC
Format=6
Find[0]=R2
Low[0]=5K
Initial[0]=10K
High[0]=20K
Find[1]=R3
Low[1]=100K
Initial[1]=470K
High[1]=1Meg
ThatCnt=10
That[0]=Equates
Function[0]=Y_Delta(V(DLVL),1,1,DCMIN,DCMAX)
POWELL_TOL=1e-4
POWELL_RelPercentTol=.1
POWELL_PercentTol=1m
HOOKE_TOL=1e-4
HOOKE_PercentTol=1m
HOOKE_RHO=.3
HOOKE_EPSILON=1e-9
HOOKE_ITERMAX=1000
DE_MAXITER=200
DE_IPRINT=50
DE_PCROS=.9
DE_FACT=.5
DE_MULTIPLIER=5
InitialRangeFactor=2
InitializeEach=False
Method=Powell
Method=Hooke
Method=LM
Method=DE
Update_Plot=False
Minimize_Plot=False
StartWith=Existing
GridSize=4
NumberOfTrys=10
Log=False
Show Log=False

[Watch]
Analysis=Transient
Format=3
ExprPercentWidth=80

[Watch]
Analysis=DC
Format=3
ExprPercentWidth=80

[WCTolerance]
Var Width=100
Nominal Width=72
Tol Width=152
Tol Name=Drift
Col Width Neq=50
Col Width Pos=50
Col Width Rnd=50

[WCFiles]
UseFile=<Library>Standard.tlib
AVAILABLE_FILE=<Library>Standard.tlib

[OPMethods]
Analysis=Transient
Standard Newton-Raphson=0,0
Source Stepping=0,0
Diagonal Gmin Stepping=0,0
Junction Gmin Stepping=0,0
Pseudo Transient=0,0

[OPMethods]
Analysis=AC
Standard Newton-Raphson=0,0
Source Stepping=0,0
Diagonal Gmin Stepping=0,0
Junction Gmin Stepping=0,0
Pseudo Transient=0,0

[OPMethods]
Analysis=DC
Standard Newton-Raphson=0,0
Source Stepping=0,0
Diagonal Gmin Stepping=0,0
Junction Gmin Stepping=0,0
Pseudo Transient=0,0

[OPMethods]
Analysis=HmDistortion
Standard Newton-Raphson=0,0
Source Stepping=0,0
Diagonal Gmin Stepping=0,0
Junction Gmin Stepping=0,0
Pseudo Transient=0,0

[OPMethods]
Analysis=ImDistortion
Standard Newton-Raphson=0,0
Source Stepping=0,0
Diagonal Gmin Stepping=0,0
Junction Gmin Stepping=0,0
Pseudo Transient=0,0

[OPMethods]
Analysis=Stability
Standard Newton-Raphson=0,0
Source Stepping=0,0
Diagonal Gmin Stepping=0,0
Junction Gmin Stepping=0,0
Pseudo Transient=0,0

[OPMethods]
Analysis=DynamicAC
Standard Newton-Raphson=0,0
Source Stepping=0,0
Diagonal Gmin Stepping=0,0
Junction Gmin Stepping=0,0
Pseudo Transient=0,0

[OPMethods]
Analysis=DynamicDC
Standard Newton-Raphson=0,0
Source Stepping=0,0
Diagonal Gmin Stepping=0,0
Junction Gmin Stepping=0,0
Pseudo Transient=0,0

[Measurements]
Analysis=DC
ShowBar=False
MRUDockID=59422
Floating=True
LocalOffset=False
Rect=426,138,468,177
Horz=-1,-1
Vert=42,39
Float=607,225
Format=3
FunctionWidth=150
TextDelim=32
GenerateExcel=False
GenerateText=False
NumberOfBranchesToDisplay=10
FileName
Expr
